fooker/mnhttn/board/mnhttn.kicad_sch

## KiCad design board/mnhttn.kicad_sch (2023-05-09)

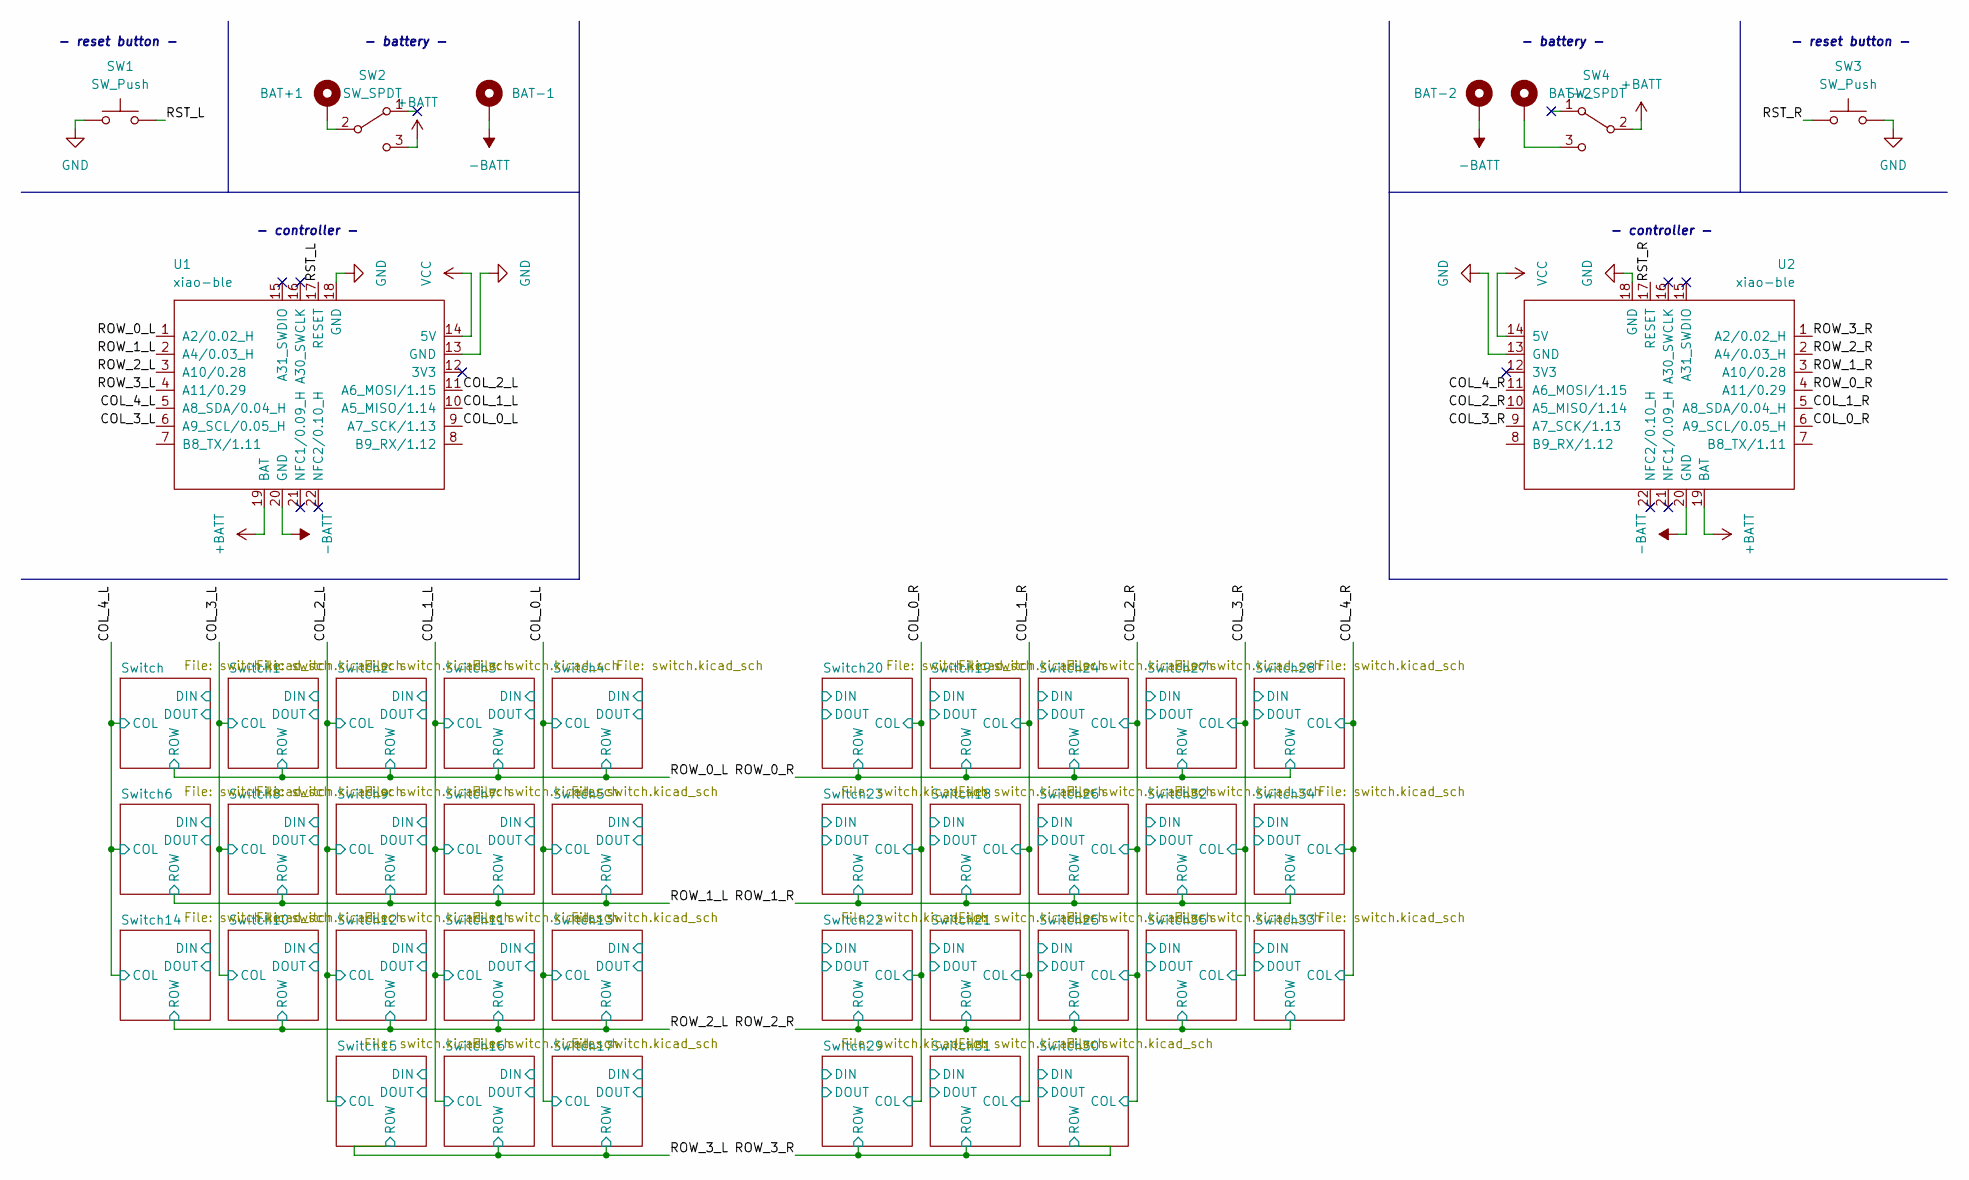
[picture p10: schematic mnhttn.kicad_sch]

Parts:
BAT+1, BAT+2: +; BatteryPad
BAT-1, BAT-2: -; BatteryPad
SW1, SW3: SW_Push; PushSwitch
SW2, SW4: SW_SPDT; MSK12C02
U1, U2: xiao-ble; xiao-ble-smd-cutout

Connections:
+BATT: SW2.3 (C), SW4.2 (B), U1.19 (BAT), U2.19 (BAT)
-BATT: BAT-1.1, BAT-2.1, U1.20 (GND), U2.20 (GND)
COL_0_L: U1.9 (A7_SCK/1.13)
COL_0_R: U2.6 (A9_SCL/0.05_H)
COL_1_L: U1.10 (A5_MISO/1.14)
COL_1_R: U2.5 (A8_SDA/0.04_H)
COL_2_L: U1.11 (A6_MOSI/1.15)
COL_2_R: U2.10 (A5_MISO/1.14)
COL_3_L: U1.6 (A9_SCL/0.05_H)
COL_3_R: U2.9 (A7_SCK/1.13)
COL_4_L: U1.5 (A8_SDA/0.04_H)
COL_4_R: U2.11 (A6_MOSI/1.15)
GND: SW1.1, SW3.1, U1.13 (GND), U1.18 (GND), U2.13 (GND), U2.18 (GND)
unnamed: BAT+1.1, SW2.2 (B)
unnamed: BAT+2.1, SW4.3 (C)
ROW_0_L: U1.1 (A2/0.02_H)
ROW_0_R: U2.4 (A11/0.29)
ROW_1_L: U1.2 (A4/0.03_H)
ROW_1_R: U2.3 (A10/0.28)
ROW_2_L: U1.3 (A10/0.28)
ROW_2_R: U2.2 (A4/0.03_H)
ROW_3_L: U1.4 (A11/0.29)
ROW_3_R: U2.1 (A2/0.02_H)
RST_L: SW1.2, U1.17 (RESET)
RST_R: SW3.2, U2.17 (RESET)
VCC: U1.14 (5V), U2.14 (5V)

Notes on the sheet:
- battery -
- reset button -
- controller -
