fooker/mnhttn/board/switch.kicad_sch

## KiCad design board/switch.kicad_sch (2023-05-17)

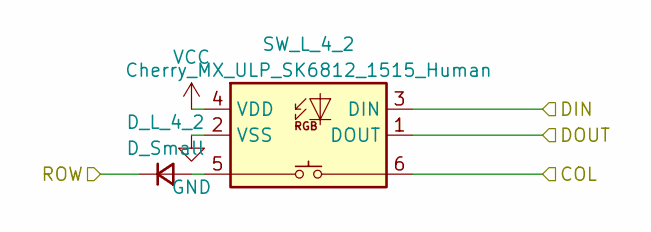
[picture p11: schematic switch.kicad_sch]

Parts:
D_L_4_2: D_Small; Diode_SOD123
SW_L_4_2: Cherry_MX_ULP_SK6812_1515_Human; Cherry_MX_ULP_Human

Connections:
COL: SW_L_4_2.6
DIN: SW_L_4_2.3 (DIN)
DOUT: SW_L_4_2.1 (DOUT)
GND: SW_L_4_2.2 (VSS)
unnamed: D_L_4_2.2 (A), SW_L_4_2.5
ROW: D_L_4_2.1 (K)
VCC: SW_L_4_2.4 (VDD)
